fdmusse/tricot-malin/img/diagram/t-shirt1_front2.png

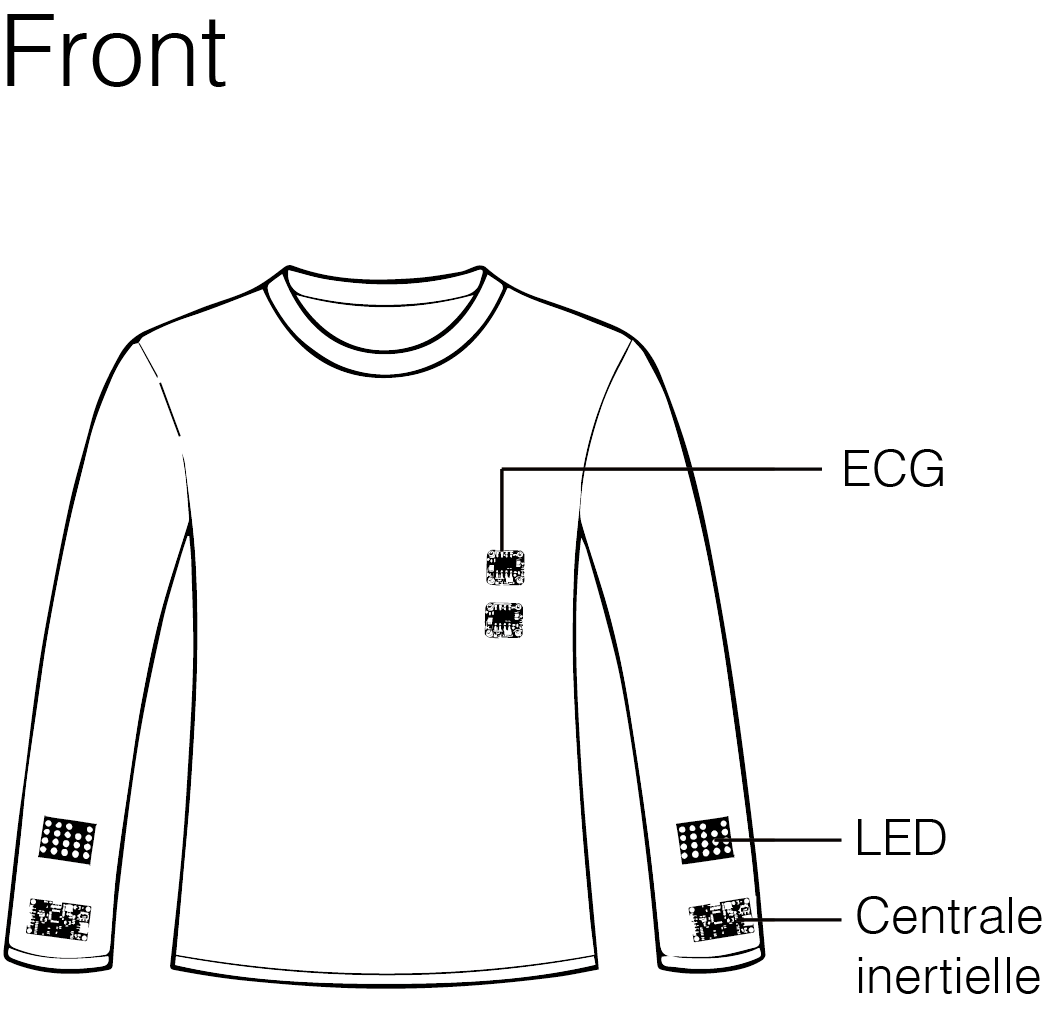
img/diagram/t-shirt1_front2.png
