fdmusse/tricot-malin/img/diagram/t-shirt_back.png

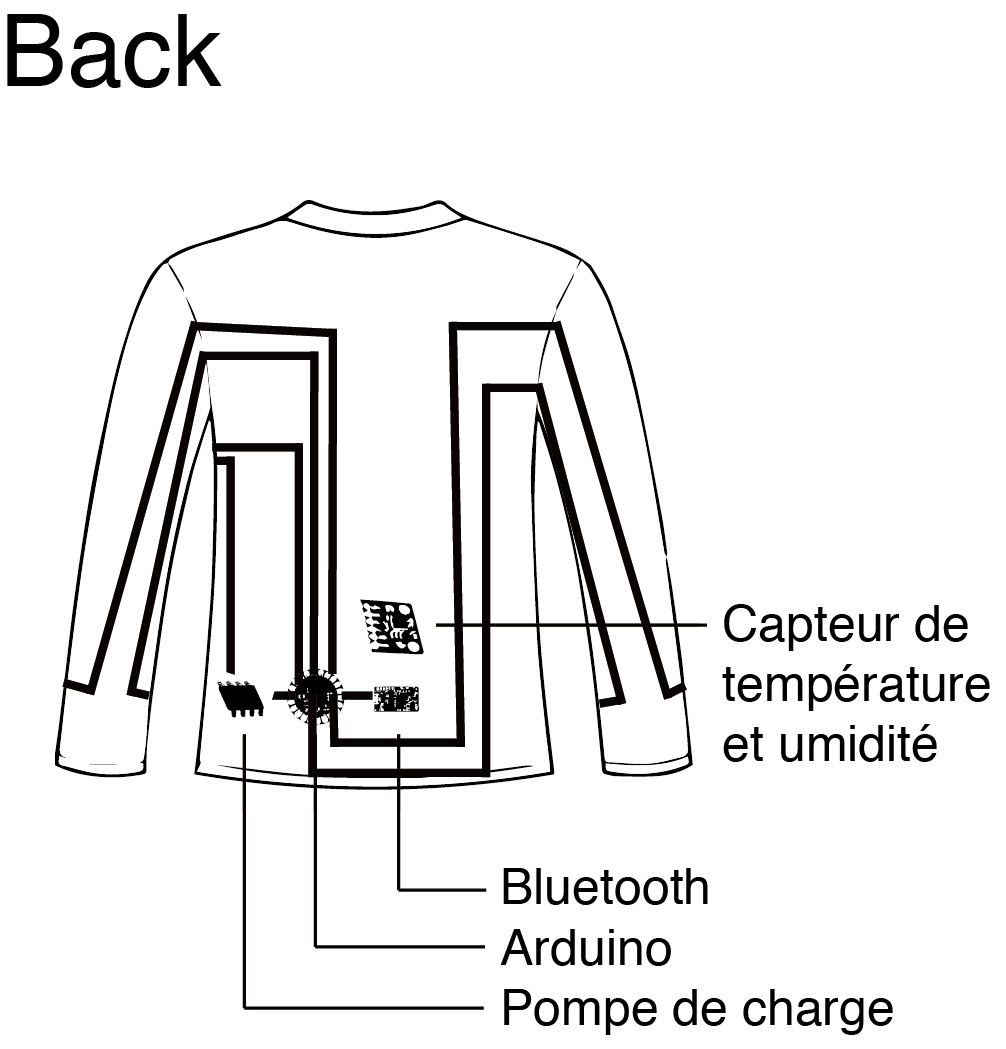
img/diagram/t-shirt_back.png
