fdmusse/tricot-malin/img/ecg/rate.jpg

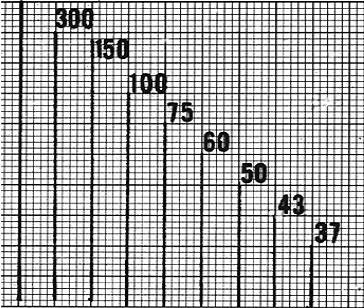
img/ecg/rate.jpg
