fdmusse/tricot-malin/processing/processing_IMU_Cube/processing_IMU_Cube.pde

import processing.serial.*;


String val;     // Data received from the serial port

String portName = Serial.list()[2]; //may need to be changed to match your port

// Create object from Serial class
Serial myPort = new Serial(this, "/dev/pts/21", 115200); //  115200 bps is the same baud rate as Arduino 


float pitch = 0.0;
float roll = 0.0;
float yaw = 0.0;
 
void setup()  { 
  size(640, 360, P3D); 
  noStroke(); 
  colorMode(RGB, 1); 
} 
 
void draw()  { 
  background(0.5);
  
  pushMatrix(); 
  translate(width/2, height/2, -30); 
  
  if (myPort.available() > 0) {
    yaw = Float.valueOf(myPort.readStringUntil('\n')).floatValue();
    pitch = Float.valueOf(myPort.readStringUntil('\n')).floatValue();
    roll = Float.valueOf(myPort.readStringUntil('\n')).floatValue();  
  }
 
  
  rotateX(pitch); 
  rotateY(-roll);
  rotateZ(yaw);
  
  
  scale(90);
  beginShape(QUADS);

  fill(0, 1, 1); vertex(-1,  1,  1);
  fill(1, 1, 1); vertex( 1,  1,  1);
  fill(1, 0, 1); vertex( 1, -1,  1);
  fill(0, 0, 1); vertex(-1, -1,  1);

  fill(1, 1, 1); vertex( 1,  1,  1);
  fill(1, 1, 0); vertex( 1,  1, -1);
  fill(1, 0, 0); vertex( 1, -1, -1);
  fill(1, 0, 1); vertex( 1, -1,  1);

  fill(1, 1, 0); vertex( 1,  1, -1);
  fill(0, 1, 0); vertex(-1,  1, -1);
  fill(0, 0, 0); vertex(-1, -1, -1);
  fill(1, 0, 0); vertex( 1, -1, -1);

  fill(0, 1, 0); vertex(-1,  1, -1);
  fill(0, 1, 1); vertex(-1,  1,  1);
  fill(0, 0, 1); vertex(-1, -1,  1);
  fill(0, 0, 0); vertex(-1, -1, -1);

  fill(0, 1, 0); vertex(-1,  1, -1);
  fill(1, 1, 0); vertex( 1,  1, -1);
  fill(1, 1, 1); vertex( 1,  1,  1);
  fill(0, 1, 1); vertex(-1,  1,  1);

  fill(0, 0, 0); vertex(-1, -1, -1);
  fill(1, 0, 0); vertex( 1, -1, -1);
  fill(1, 0, 1); vertex( 1, -1,  1);
  fill(0, 0, 1); vertex(-1, -1,  1);

  endShape();
  
  popMatrix(); 
  
} 
