fdmusse/tricot-malin/arduino/IMU_getOrientation_simple/IMU_getOrientation.ino

// The SFE_LSM9DS0 requires both the SPI and Wire libraries.
// Unfortunately, you'll need to include both in the Arduino
// sketch, before including the SFE_LSM9DS0 library.
#include <SPI.h> // Included for SFE_LSM9DS0 library
#include <Wire.h>
#include <SFE_LSM9DS0.h>

///////////////////////
// Example I2C Setup //
///////////////////////
// Comment out this section if you're using SPI
// SDO_XM and SDO_G are both grounded, so our addresses are:
#define LSM9DS0_XM  0x1D // Would be 0x1E if SDO_XM is LOW
#define LSM9DS0_G   0x6B // Would be 0x6A if SDO_G is LOW
// Create an instance of the LSM9DS0 library called `dof` the
// parameters for this constructor are:
// [SPI or I2C Mode declaration],[gyro I2C address],[xm I2C add.]
LSM9DS0 dof(MODE_I2C, LSM9DS0_G, LSM9DS0_XM);


#define PRINT_CALCULATED
//#define PRINT_RAW

#define PRINT_SPEED 500 // 500 ms between prints

void setup() {
  // put your setup code here, to run once:
  Serial.begin(115200); // Start serial at 115200 bps
  // Use the begin() function to initialize the LSM9DS0 library.
  // You can either call it with no parameters (the easy way):
  uint16_t status = dof.begin();

}

void loop() {
  // put your main code here, to run repeatedly:
  dof.readGyro();
  dof.readAccel();
  dof.readMag();
  
  printOrientation(dof.calcAccel(dof.ax), dof.calcAccel(dof.ay), 
                   dof.calcAccel(dof.az));
                   
   Serial.println();
  
  delay(PRINT_SPEED);
}

// Another fun function that does calculations based on the
// acclerometer data. This function will print your LSM9DS0's
// orientation -- it's roll and pitch angles.
void printOrientation(float x, float y, float z)
{
  float pitch, roll;
  
  pitch = atan2(x, sqrt(y * y) + (z * z));
  roll = atan2(y, sqrt(x * x) + (z * z));

  Serial.print(pitch, 2);
  Serial.print(",");
  Serial.println(roll, 2);
}
